segozcan/Mind-The-Cap/2-Design/3-PCB/FlybackConverter_v2/aaasdsad.png

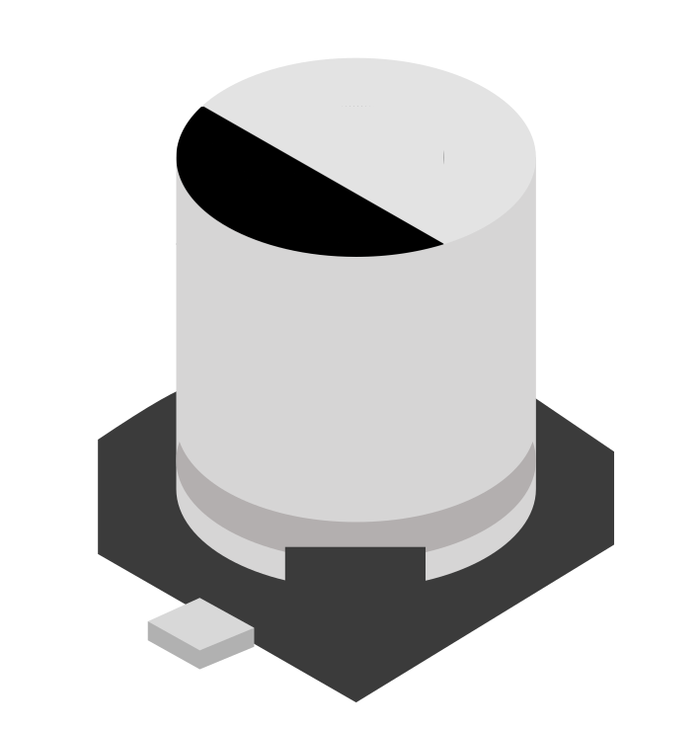
2-Design/3-PCB/FlybackConverter_v2/aaasdsad.png
