segozcan/Mind-The-Cap/2-Design/5-3DModel/final-1.png

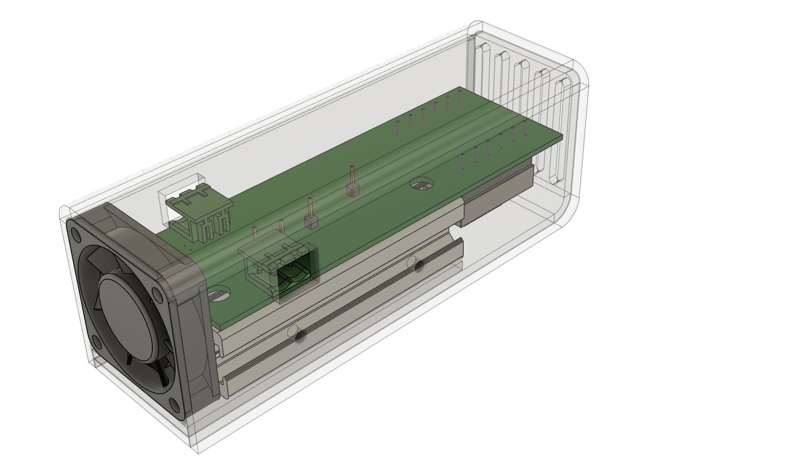
2-Design/5-3DModel/final-1.png
