segozcan/Mind-The-Cap/2-Design/5-3DModel/flat.png

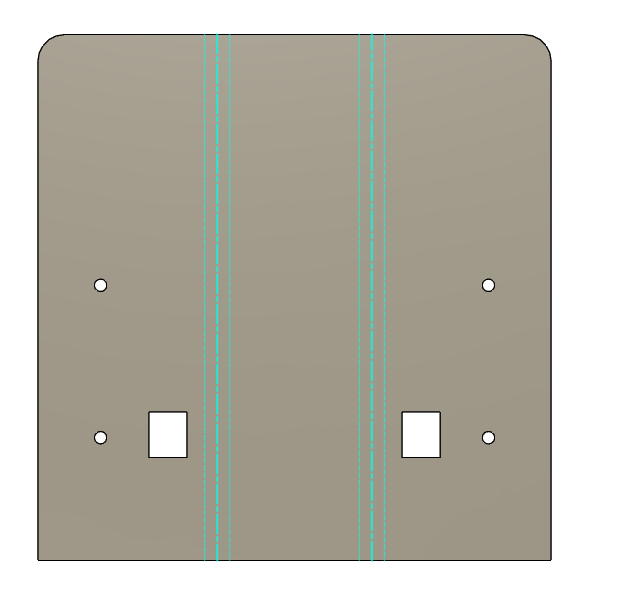
2-Design/5-3DModel/flat.png
