segozcan/Mind-The-Cap/2-Design/5-3DModel/laser.png

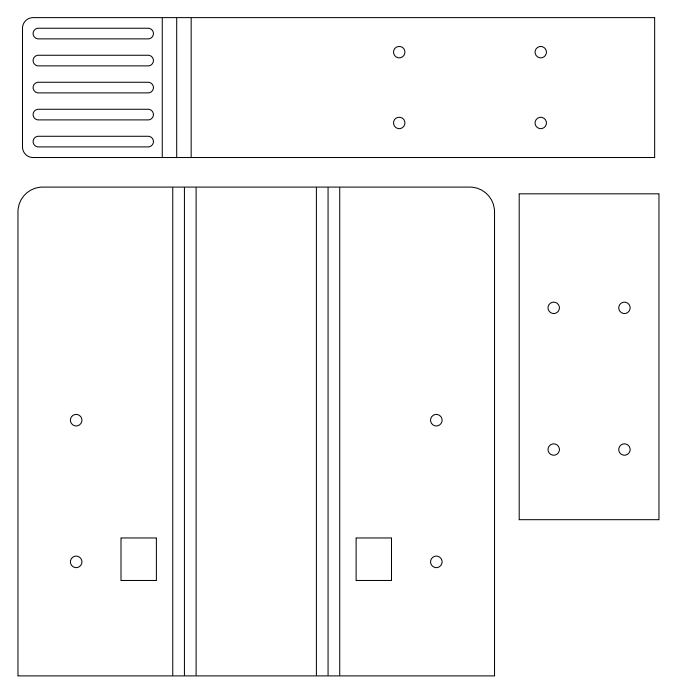
2-Design/5-3DModel/laser.png
