segozcan/Mind-The-Cap/4-Report/final_report/img/int_w.jpg

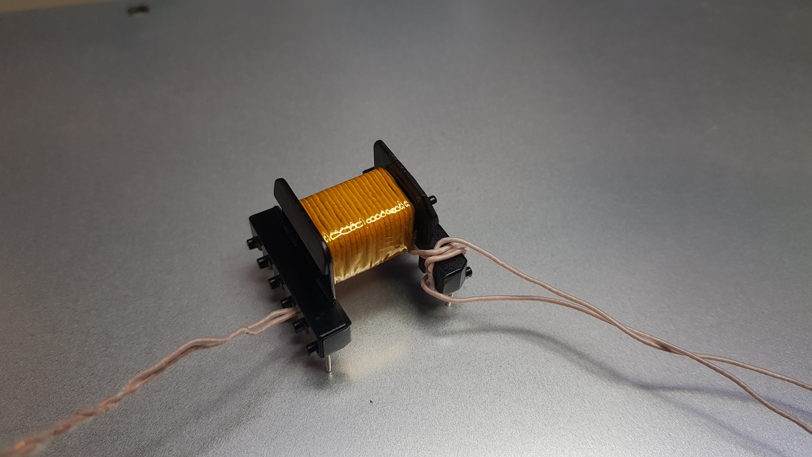
4-Report/final_report/img/int_w.jpg
