segozcan/Mind-The-Cap/1-Simulation/2-Simple_Flyback/Flyback_v4.asc

C1: cap; 10n
C2: cap; 20p
C_o: cap; 2.6µ; Rser=30m
D1: diode
D2: diode
D_f: diode
D_TVS: diode; MyTVS
L1: ind; 0.12µ
L_p: ind2; 12µ; Rser=4.4m
L_s: ind2; 192µ; Rser=71.2m
L_spice_magic: ind; 1p; Rser=3m
R1: res; 220
R_G: res; 2.2
R_L: res; 48
R_spice_magic: res; 1Meg
SW: nmos; IPT015N10N5
V_drive: voltage; PULSE(0 5 0 1n 1n 2.7u 5u)
V_s: voltage; 12V
Named nets: 0, V_G
k L_p L_s 1
----------------------
 
 
----------------------
Converter
Driver
.tran 0 20m 18m 0.01
.model Dideal D(Ron=0.0001 Roff=100G Vfwd=0)
R_Pri = 4.4 mOhm
R_Sec = 71.2 mOhm
.model MyTVS d Ron=10m Vfwd=1000 Vrev=30 Epsilon=1 RevEpsilon=1
