segozcan/Mind-The-Cap/1-Simulation/1-Transformer_Modelling/Transformer_Magnetic_Model.asc

L_p: ind2; 33µ; Rser=1m
L_s: ind2; 33µ; Rser=1m
R_s: res; 10
V_s: voltage; SINE(0 5 50)
Named nets: 0
k L_p L_s 1
----------------------
 
 
----------------------
.tran 0 5 4.9
